amskje/Delta-Robot/RaspberryPi/pictures/twist/banan.png

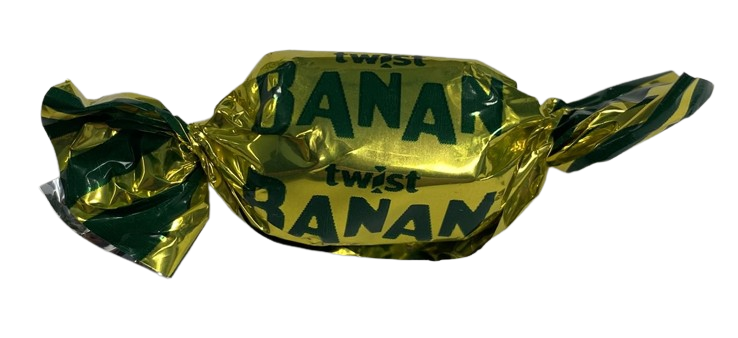
RaspberryPi/pictures/twist/banan.png
