amskje/Delta-Robot/RaspberryPi/pictures/twist/cocos.png

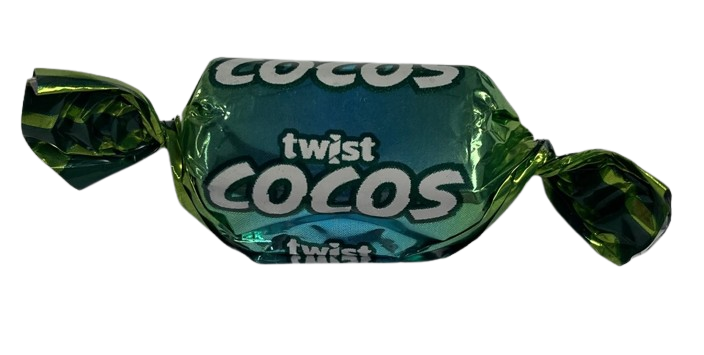
RaspberryPi/pictures/twist/cocos.png
