amskje/Delta-Robot/RaspberryPi/pictures/twist/crisp.png

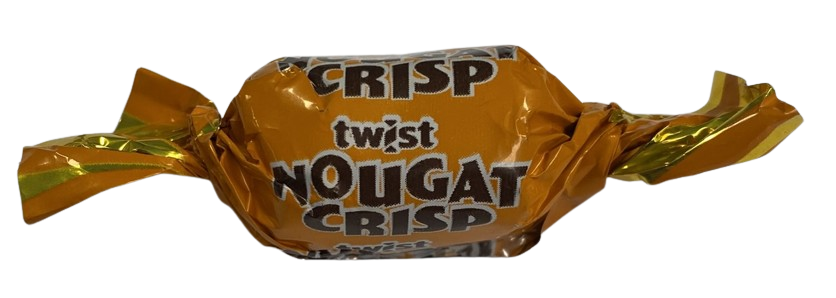
RaspberryPi/pictures/twist/crisp.png
