amskje/Delta-Robot/RaspberryPi/pictures/twist/daim.png

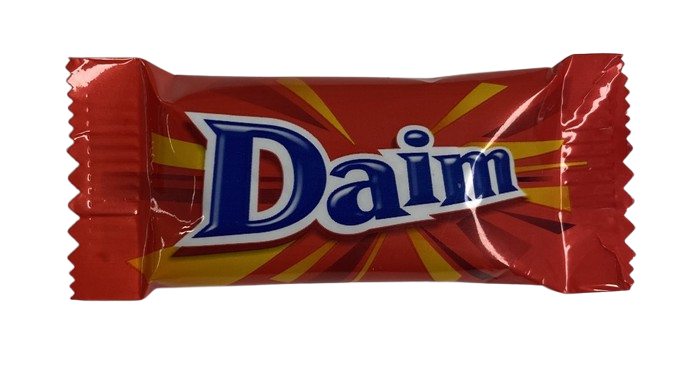
RaspberryPi/pictures/twist/daim.png
