amskje/Delta-Robot/RaspberryPi/pictures/twist/eclairs.png

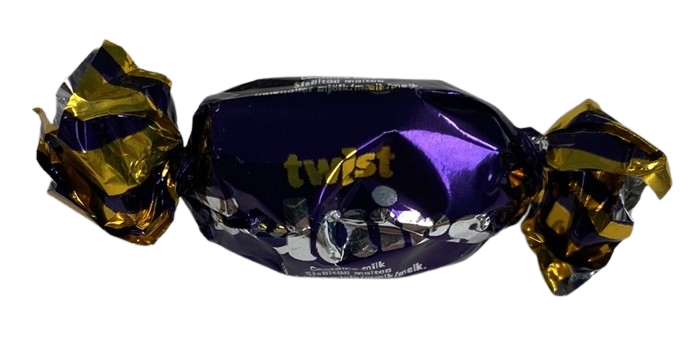
RaspberryPi/pictures/twist/eclairs.png
