amskje/Delta-Robot/RaspberryPi/pictures/twist/fransk.png

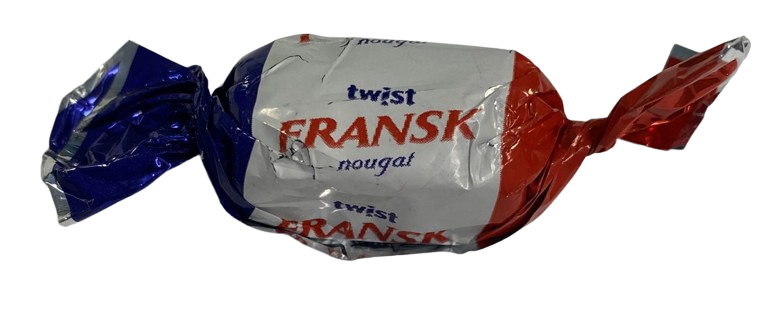
RaspberryPi/pictures/twist/fransk.png
