amskje/Delta-Robot/RaspberryPi/pictures/twist/golden.png

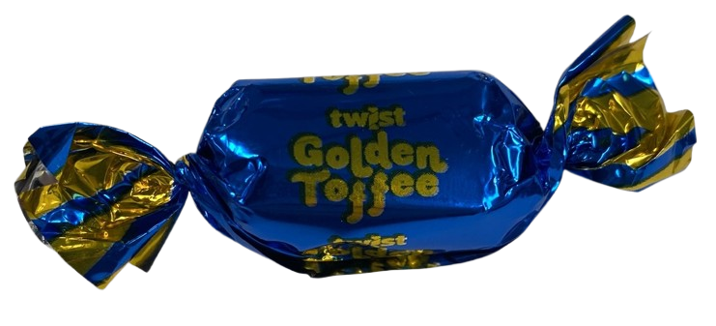
RaspberryPi/pictures/twist/golden.png
