amskje/Delta-Robot/RaspberryPi/pictures/twist/japp.png

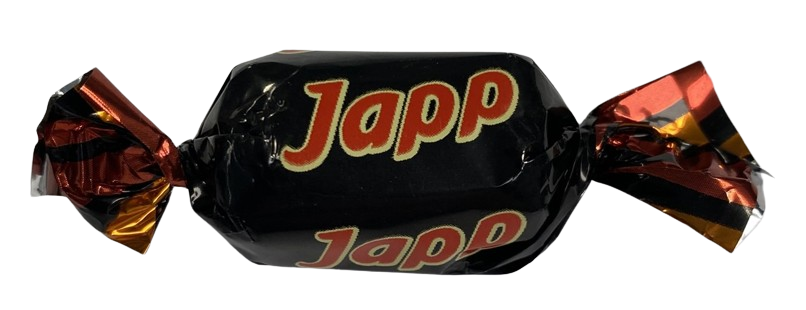
RaspberryPi/pictures/twist/japp.png
