amskje/Delta-Robot/RaspberryPi/pictures/twist/karamell.png

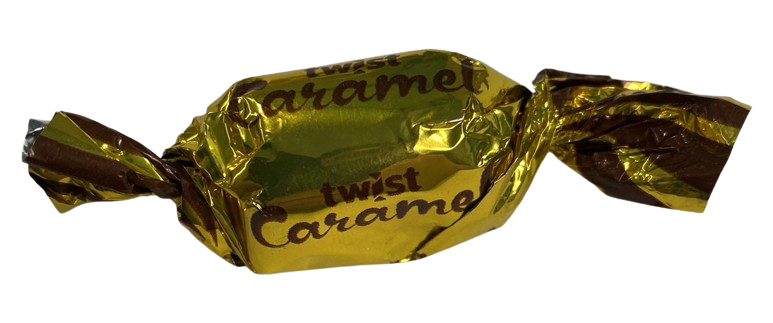
RaspberryPi/pictures/twist/karamell.png
