amskje/Delta-Robot/RaspberryPi/pictures/twist/lakris.png

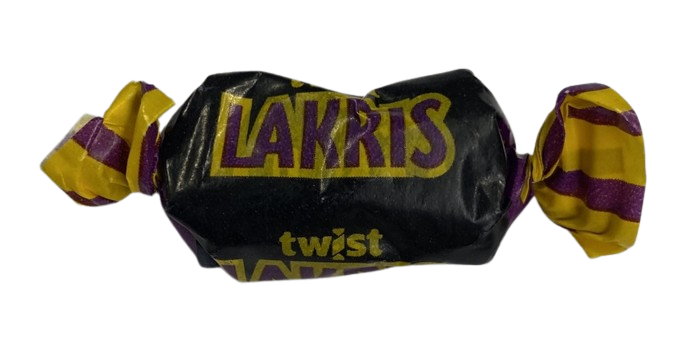
RaspberryPi/pictures/twist/lakris.png
