amskje/Delta-Robot/RaspberryPi/pictures/twist/marsipan.png

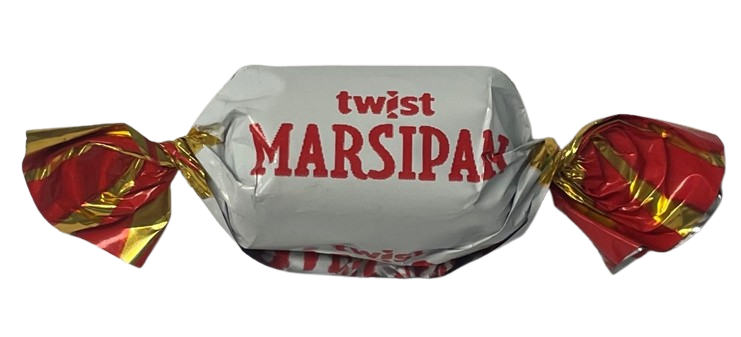
RaspberryPi/pictures/twist/marsipan.png
