amskje/Delta-Robot/RaspberryPi/pictures/twist/notti.png

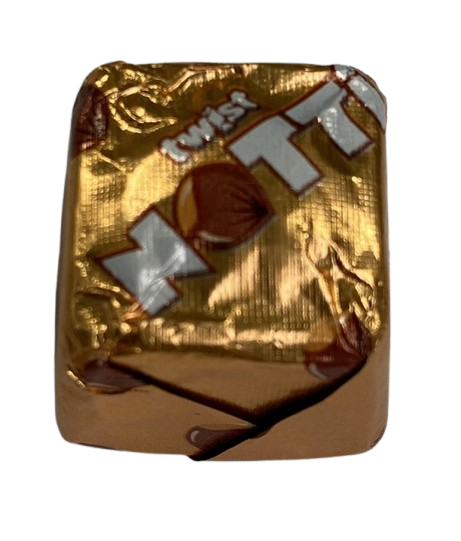
RaspberryPi/pictures/twist/notti.png
