amskje/Delta-Robot/RaspberryPi/pictures/twist/toffee.png

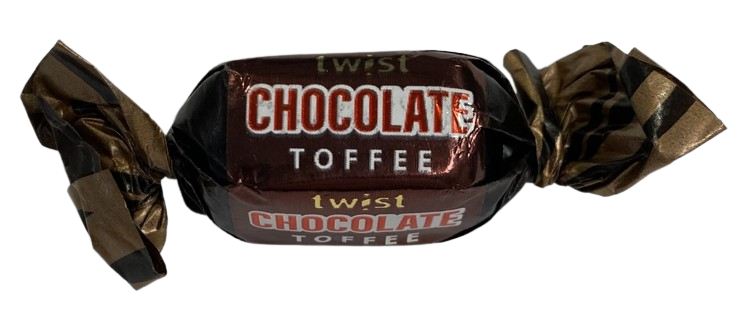
RaspberryPi/pictures/twist/toffee.png
