amskje/Delta-Robot/3D models/Heimelaga deler (.stl)/Kamera casing/Kamera casing del 2 V1.STL

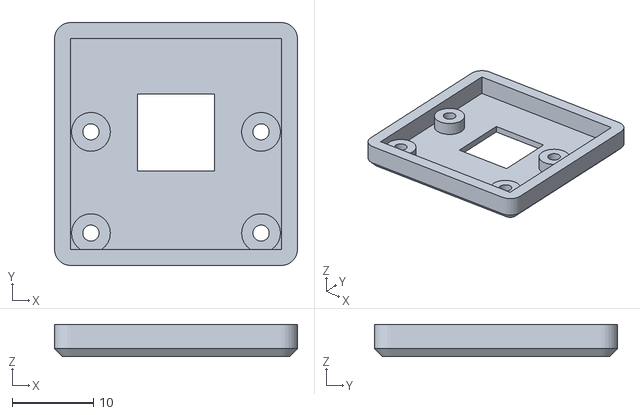
[picture p30: CAD file, 2025-08-12]
3D models/Heimelaga deler (.stl)/Kamera casing/Kamera casing del 2 V1.STL
30.0 x 30.0 x 4.00
