amskje/Delta-Robot/3D models/Heimelaga deler (.stl)/Powerswitch/PowerswitchV2.stl

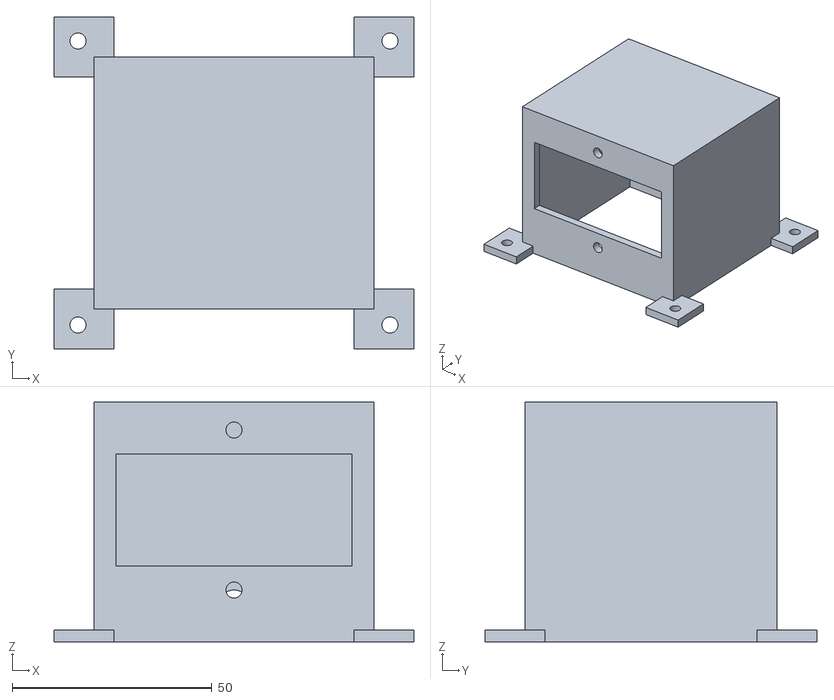
[picture p31: CAD file, 2025-08-12]
3D models/Heimelaga deler (.stl)/Powerswitch/PowerswitchV2.stl
90.0 x 83.0 x 60.0
