amskje/Delta-Robot/3D models/Heimelaga deler (.stl)/Skjermcasing/Skjermcasing stand V1.stl

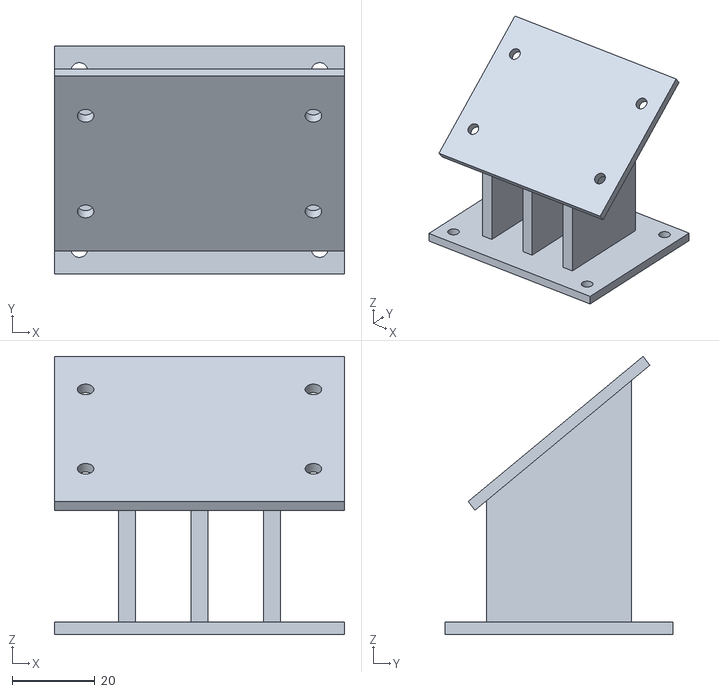
[picture p32: CAD file, 2025-08-12]
3D models/Heimelaga deler (.stl)/Skjermcasing/Skjermcasing stand V1.stl
70.0 x 55.0 x 67.2
