amskje/Delta-Robot/3D models/Heimelaga deler (.stl)/Underlag/slange-ledning-feste.stl

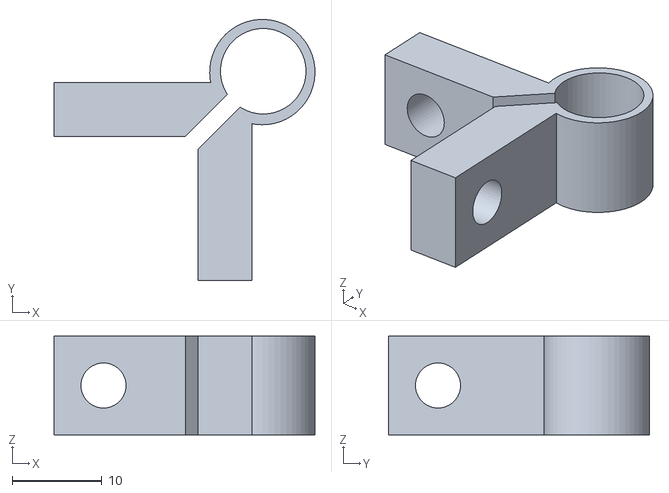
[picture p33: CAD file, 2025-08-12]
3D models/Heimelaga deler (.stl)/Underlag/slange-ledning-feste.stl
29.0 x 29.0 x 11.0
