amskje/Delta-Robot/3D models/Heimelaga deler (.stl)/Vakuumpumpe casing/Vakuumpumpe casingV1.stl

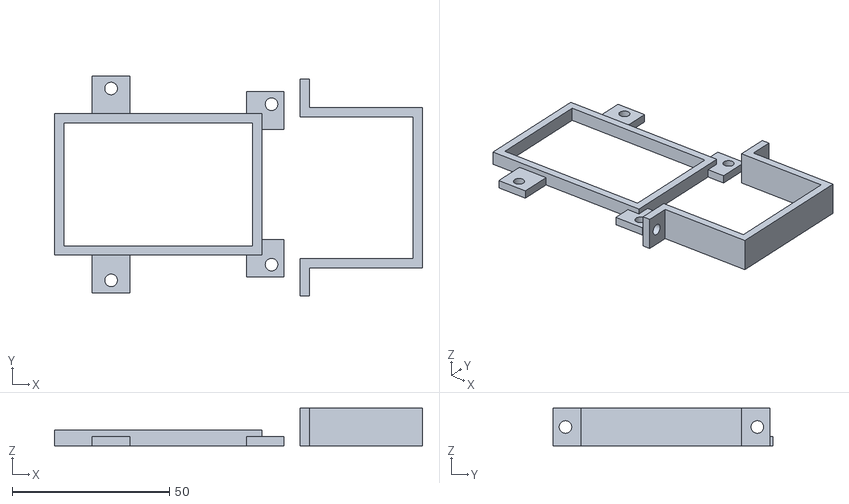
[picture p34: CAD file, 2025-08-12]
3D models/Heimelaga deler (.stl)/Vakuumpumpe casing/Vakuumpumpe casingV1.stl
117.0 x 70.0 x 12.0
