amskje/Delta-Robot/3D models/Heimelaga deler (.stl)/Bicep/BicepOriginial.STL

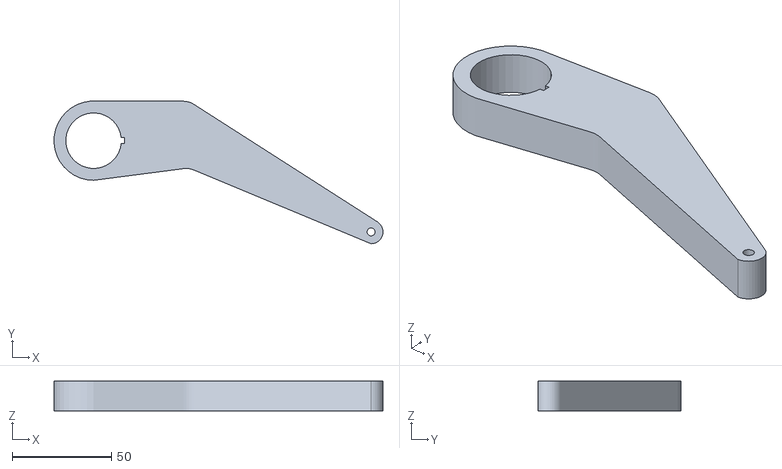
[picture p35: CAD file, 2025-08-12]
3D models/Heimelaga deler (.stl)/Bicep/BicepOriginial.STL
166.0 x 71.9 x 15.0
