amskje/Delta-Robot/3D models/Heimelaga deler (.stl)/Skjermcasing/Skjermcasing skinne V1.stl

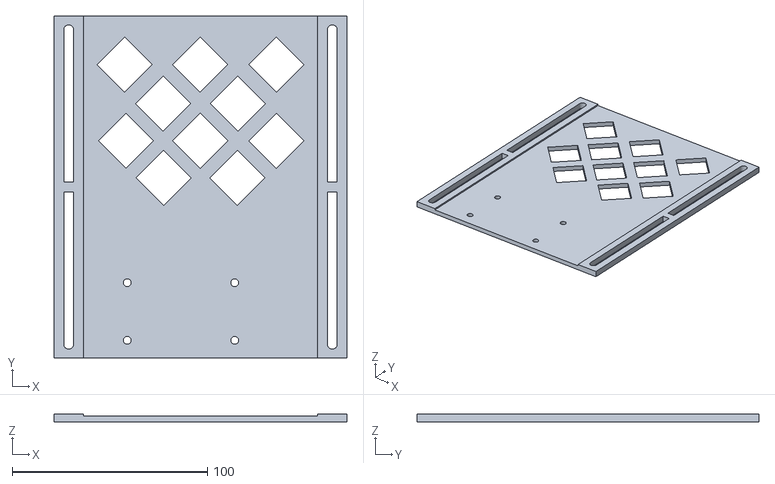
[picture p36: CAD file, 2025-08-12]
3D models/Heimelaga deler (.stl)/Skjermcasing/Skjermcasing skinne V1.stl
150.0 x 175.0 x 4.00
