amskje/Delta-Robot/3D models/Heimelaga deler (.stl)/Skjermcasing/Skjermcasing RPi side V3.stl

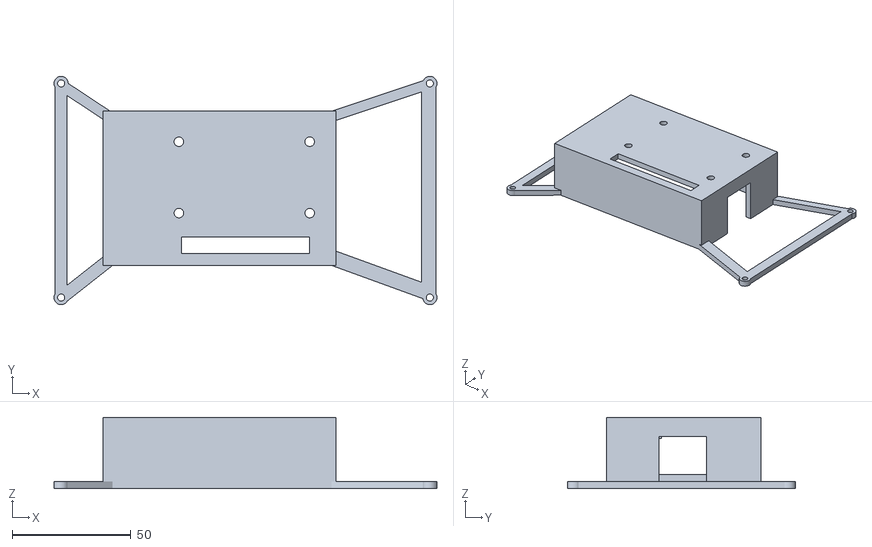
[picture p37: CAD file, 2025-08-12]
3D models/Heimelaga deler (.stl)/Skjermcasing/Skjermcasing RPi side V3.stl
161.0 x 96.0 x 30.0
