amskje/Delta-Robot/Calibration/Camera_calibration/calibration_images/chessboard_frame3.jpg

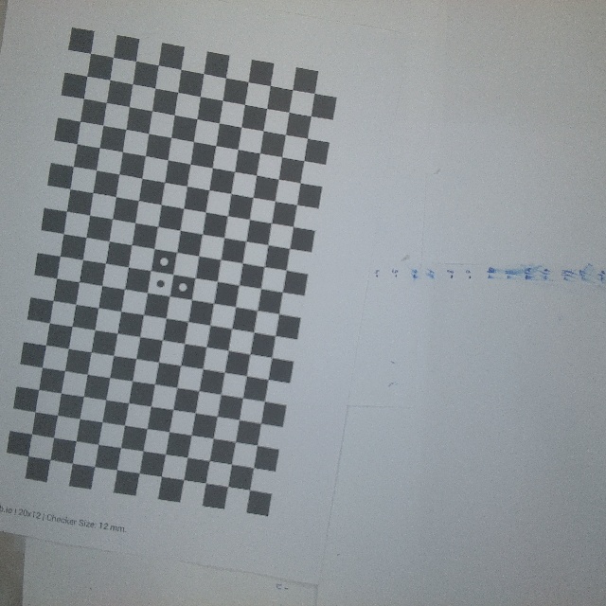
Calibration/Camera_calibration/calibration_images/chessboard_frame3.jpg
