amskje/Delta-Robot/Calibration/Camera_calibration/calibration_images/chessboard_frame13.jpg

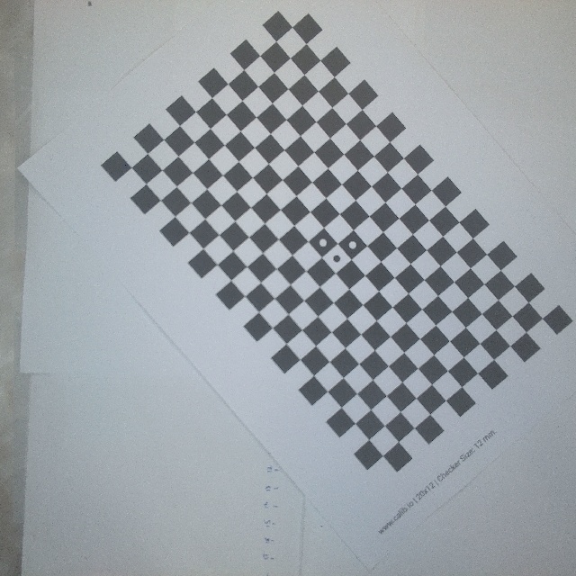
Calibration/Camera_calibration/calibration_images/chessboard_frame13.jpg
