amskje/Delta-Robot/Calibration/Camera_calibration/calibration_images/chessboard_frame16.jpg

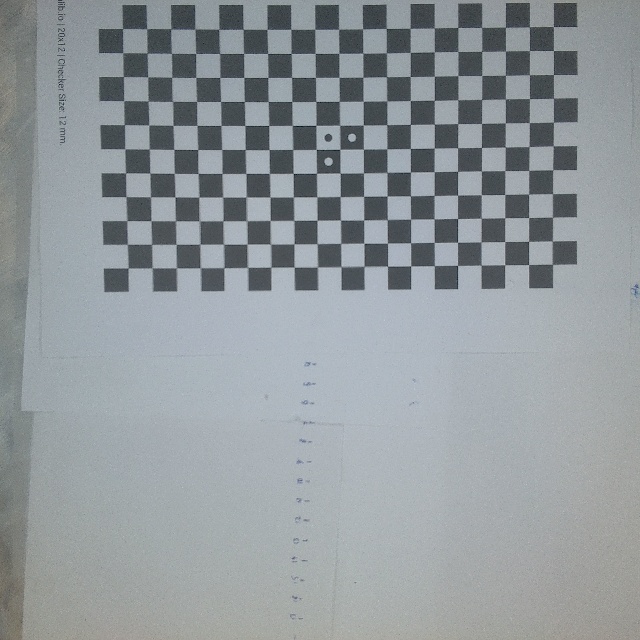
Calibration/Camera_calibration/calibration_images/chessboard_frame16.jpg
