amskje/Delta-Robot/Calibration/Camera_calibration/calibration_images/chessboard_frame.jpg

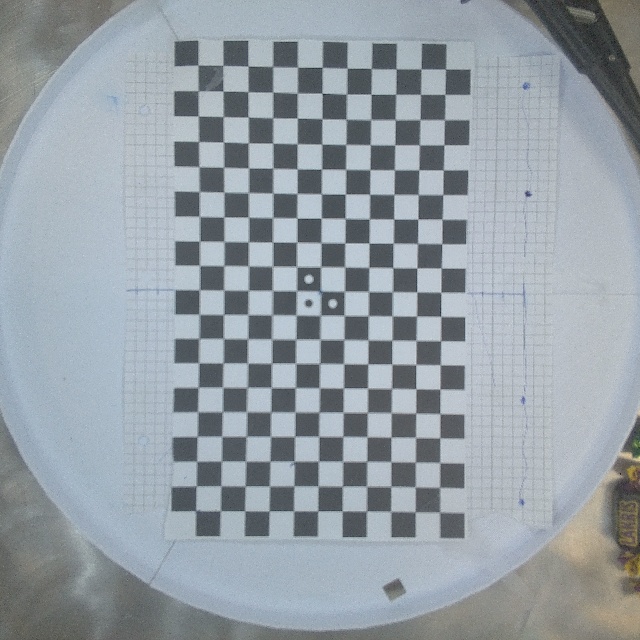
Calibration/Camera_calibration/calibration_images/chessboard_frame.jpg
